ytsurui/SwitchDecoder3/Firmware/sw_config.c

/*
 * sw_config.c
 *
 * Created: 2022/09/16 23:22:58
 *  Author: Y.Tsurui
 */ 

#include <avr/io.h>
#include <avr/eeprom.h>

uint8_t __attribute__((section(".eeprom"))) val[] =
{
	0xFF,	// Configure Area
	0x81,	// Addr1 (Low)
	0xF8,	// Addr2 (High)
	0x3F,	// Turn-On Time Low-Byte
	0x00,	// Turn-On Time High-Byte
	0x00,	// Turn-On Delay Time Low-Byte
	0x00,	// Turn-On Delay Time High-Byte
	0x00,	// Configure Bits
	0xD0,	// Lock Time Low-Byte
	0x07,	// Lock Time High-Byte	(0x07D0 = 3000 / 2.000sec)
	0x88,	// Switch Auto-Move Time Low-Byte
	0x13,	// Switch Auto-Move Time High-Byte (0x1388 = 5000 / 5.000sec)
	0x01,	// Switch Direction LED enable/disable (0=disable / 1=enable)
};

uint8_t addrInfo[2];
uint8_t turnOnTime[2];
uint8_t turnOnDelayTime[2];
uint8_t configureBits;

uint8_t SwitchLockTime[2];
uint8_t SwitchAutoMoveTime[2];

uint8_t SwitchLEDenable;

#define FIRMWARE_VERSION_CODE	5
#define MANUFACTURE_ID	13

uint8_t addr_1byte_write_cache;
uint8_t addr_2byte_write_cache;
uint8_t lastStat_cache;

uint8_t cvReadCount;

uint8_t read_cv_raw(uint8_t CVnum)
{
	return (eeprom_read_byte(val + CVnum));
}

void write_eeprom(uint8_t CVnum, uint8_t data)
{
	eeprom_busy_wait();
	eeprom_update_byte(val + CVnum, data);
}

void initCV(void)
{
	write_eeprom(1, 0x81);
	write_eeprom(2, 0xF8);
	write_eeprom(3, 0x3F);
	write_eeprom(4, 0x00);
	write_eeprom(5, 0x00);
	write_eeprom(6, 0x00);
	write_eeprom(7, 0x00);
	write_eeprom(8, 0xD0);
	write_eeprom(9, 0x07);
	write_eeprom(10, 0x88);
	write_eeprom(11, 0x13);
	write_eeprom(12, 0x01);
	
	// Write Init Flag
	write_eeprom(0, 0);
	
	//initConfig();
}

void initConfig(void)
{
	uint8_t cfgInfo;
	
	//eeprom_busy_wait();
	
	cfgInfo = read_cv_raw(0);
	
	if (cfgInfo == 0xFF) {
		initCV();
		eeprom_busy_wait();
	}
	
	/*
	addrInfo[0] = read_cv_raw(1);
	addrInfo[1] = read_cv_raw(2);
	turnOnTime[0] = read_cv_raw(3);
	turnOnTime[1] = read_cv_raw(4);
	turnOnDelayTime[0] = read_cv_raw(5);
	turnOnDelayTime[1] = read_cv_raw(6);
	configureBits = read_cv_raw(7);
	*/	
	cvReadCount = 0;
}

uint8_t loadCVevent(void)
{
	if (cvReadCount == 0) {
		addrInfo[0] = read_cv_raw(1);
	} else if (cvReadCount == 1) {
		addrInfo[1] = read_cv_raw(2);
	} else if (cvReadCount == 2) {
		turnOnTime[0] = read_cv_raw(3);
	} else if (cvReadCount == 3) {
		turnOnTime[1] = read_cv_raw(4);
	} else if (cvReadCount == 4) {
		turnOnDelayTime[0] = read_cv_raw(5);
	} else if (cvReadCount == 5) {
		turnOnDelayTime[1] = read_cv_raw(6);
	} else if (cvReadCount == 6) {
		configureBits = read_cv_raw(7);
	} else if (cvReadCount == 7) {
		SwitchLockTime[0] = read_cv_raw(8);
	} else if (cvReadCount == 8) {
		SwitchLockTime[1] = read_cv_raw(9);
	} else if (cvReadCount == 9) {
		SwitchAutoMoveTime[0] = read_cv_raw(10);
	} else if (cvReadCount == 10) {
		SwitchAutoMoveTime[1] = read_cv_raw(11);
	} else if (cvReadCount == 11) {
		SwitchLEDenable = read_cv_raw(12);
	}
	
	cvReadCount++;
	if (cvReadCount > 11) {
		return 0;
	} 
	return 1;
}

uint8_t read_cv_byte(uint16_t CVnum)
{
	switch (CVnum) {
		case 7:
			return FIRMWARE_VERSION_CODE;
		case 8:
			return MANUFACTURE_ID;
		case 1:
			return addrInfo[0];
		case 9:
			return addrInfo[1];
		case 34:
			return turnOnTime[0];
		case 35:
			return turnOnTime[1];
		case 36:
			return turnOnDelayTime[0];
		case 37:
			return turnOnDelayTime[1];
		case 33:
			return configureBits;
		case 39:
			return SwitchLockTime[0];
		case 40:
			return SwitchLockTime[1];
		case 41:
			return SwitchAutoMoveTime[0];
		case 42:
			return SwitchAutoMoveTime[1];
		case 43:
			return SwitchLEDenable;
	}
	
	return 0xFF;
}

void write_cv_byte(uint16_t CVnum, uint8_t data)
{
	uint8_t eepromAddr = 0;
	
	switch (CVnum) {
		case 7:
			// Version ID, read-only
			return;
		case 8:
			// Manufacture ID, Reset
			if ((data == MANUFACTURE_ID) || (data == 8)) {
				write_eeprom(0, 0xFF);
				initCV();
			}
			return;
		case 1:
			// Decoder Address LSB
			addrInfo[0] = data;
			eepromAddr = 1;
			break;
		case 9:
			// Decoder Address MSB
			addrInfo[1] = data;
			eepromAddr = 2;
			break;
		case 34:
			// Turn-On Time LSB
			turnOnTime[0] = data;
			eepromAddr = 3;
			break;
		case 35:
			// Turn-On Time MSB
			turnOnTime[1] = data;
			eepromAddr = 4;
			break;
		case 36:
			// Turn-On Delay Time LSB
			turnOnDelayTime[0] = data;
			eepromAddr = 5;
			break;
		case 37:
			// Turn-On Delay Time MSB
			turnOnDelayTime[1] = data;
			eepromAddr = 6;
			break;
		case 33:
			// Decoder Configure Bits
			configureBits = data;
			eepromAddr = 7;
			break;
		case 39:
			// Switch Lock Time LSB
			SwitchLockTime[0] = data;
			eepromAddr = 8;
			break;
		case 40:
			// Switch Lock Time MSB
			SwitchLockTime[1] = data;
			eepromAddr = 9;
			break;
		case 41:
			// Switch Auto-Move Type LSB
			SwitchAutoMoveTime[0] = data;
			eepromAddr = 10;
			break;
		case 42:
			SwitchAutoMoveTime[1] = data;
			eepromAddr = 11;
			break;
		case 43:
			// Switch Direction LED enable or disable
			SwitchLEDenable = data;
			eepromAddr = 12;
			break;
	}
	
	if (eepromAddr > 0) {
		eeprom_busy_wait();
		write_eeprom(eepromAddr, data);
		eeprom_busy_wait();
	}
	
	return;
}


uint8_t chk_addr(uint8_t addr1_data, uint8_t addr2_data)
{
	addr2_data &= 0xFE;
	
	if ((addr1_data == addrInfo[0]) && (addr2_data == addrInfo[1])) {
		return (0xFF);
	} else {
		return (0x00);
	}
}

uint8_t write_addr(uint8_t addr1_data, uint8_t addr2_data)
{
	uint8_t stat;
	
	stat = addr2_data & 0x01;
	addr2_data &= 0xFE;
	addr2_data |= 0x08;
		
	if ((addr1_data == addr_1byte_write_cache) && (addr2_data == addr_2byte_write_cache)) {
		if (stat != lastStat_cache) {
			eeprom_busy_wait();
			//eeprom_write_byte(&addr_1byte_eemem, addr1_data);
			//eeprom_write_byte(&addr_2byte_eemem, addr2_data);
		
			write_eeprom(1, addr1_data);
			write_eeprom(2, addr2_data);
		
			addrInfo[0] = addr1_data;
			addrInfo[1] = addr2_data;
			eeprom_busy_wait();
			return (0xFF);
		} else {
			return 0x00;
		}
	} else {
		addr_1byte_write_cache = addr1_data;
		addr_2byte_write_cache = addr2_data;
		lastStat_cache = stat;		
		return (0x00);
	}
}

uint16_t getTurnOnTime(void)
{
	return (uint16_t)(turnOnTime[1] << 8) + turnOnTime[0];
}

uint16_t getTurnOnDelayTime(void)
{
	return (uint16_t)(turnOnDelayTime[1] << 8) + turnOnDelayTime[0];
}

uint8_t getConfigureBytes(void)
{
	return configureBits;
}

uint16_t getLockTime(void)
{
	return (uint16_t)(SwitchLockTime[1] << 8) + SwitchLockTime[0];
}

uint16_t getAutoMoveTime(void)
{
	return (uint16_t)(SwitchAutoMoveTime[1] << 8) + SwitchAutoMoveTime[0];
}

uint8_t getDirectionLEDenable(void)
{
	return (SwitchLEDenable);
}
