ytsurui/SwitchDecoder3/Firmware/prog_port.h

/*
 * prog_port.h
 *
 * Created: 2022/09/17 0:57:56
 *  Author: Y.Tsurui
 */ 

void initProgPort(void);
void clkReceiverProgPort(void);
void taskProgMode(void);
uint8_t readProgMode(void);
void clearProgMode(void);

uint8_t readLockStat(void);
