ytsurui/SwitchDecoder3/Firmware/cpuclk_avr0.c

/*
 * cpuclk.c
 *
 * Created: 2021/01/25 10:04:40
 *  Author: Y.Tsurui
 */ 

#include <avr/io.h>
#include <avr/cpufunc.h>

void setCLK(void)
{
	// Clock Configuration (10MHz)
	//CCP = CCP_IOREG_gc;
	//CLKCTRL.MCLKCTRLB = 0x01;	// Prescaler Enable, prescale=2 (10MHz)
	ccp_write_io((void *) & (CLKCTRL.MCLKCTRLB), CLKCTRL_PDIV_2X_gc | CLKCTRL_PEN_bm);
	
	// BOD Enable
	//BOD.CTRLA = BOD_ACTIVE_ENABLED_gc;
	//BOD.CTRLB = BOD_LVL_BODLEVEL0_gc; 
	ccp_write_io((void *) & (BOD.CTRLA), BOD_ACTIVE_ENABLED_gc);
	ccp_write_io((void *) & (BOD.CTRLB), BOD_LVL_BODLEVEL0_gc);
}
