ytsurui/SwitchDecoder3/Firmware/dcc_prog_mode.h

/*
 * dcc_prog_mode.h
 *
 * Created: 2022/09/17 1:42:50
 *  Author: ytsurui
 */ 

void dccProgPageMode(uint8_t packetLength, uint8_t packetData[]);
void dccProgDirectMode(uint8_t packetLength, uint8_t packetData[]);
